Vichayasan/controller-AE-kit/Firmware/logo_mod.py

# logo_mod.py - Startup logo converted from logo.png for ST7567 128x64 LCD

try:
    import time
except ImportError:
    time = None

LOGO_W = 64
TEXT_X = 68
TEXT_Y = 17
TEXT_GAP = 8

LOGO_LEFT_BITMAP = bytes((
    0x00, 0x00, 0x00, 0x00, 0x00, 0x00, 0x00, 0x00, 0x00, 0x00, 0x00, 0x00, 0x00, 0x00, 0x00, 0x00,
    0x00, 0x00, 0x00, 0x00, 0x00, 0x00, 0x00, 0x00, 0x00, 0x00, 0x00, 0x00, 0x00, 0x00, 0x00, 0x00,
    0x00, 0x00, 0x00, 0x00, 0x00, 0x00, 0x00, 0x00, 0x00, 0x00, 0x00, 0x00, 0x00, 0x00, 0x00, 0x00,
    0x00, 0x00, 0x00, 0x00, 0x00, 0x00, 0x00, 0x00, 0x00, 0x00, 0x00, 0x00, 0x00, 0x00, 0x00, 0x00,
    0x00, 0x00, 0x00, 0x00, 0x00, 0x00, 0x00, 0x00, 0x00, 0x00, 0x00, 0x00, 0x00, 0x80, 0xC0, 0xE0,
    0xE0, 0xC0, 0x80, 0x80, 0x00, 0x00, 0x00, 0x00, 0x00, 0x30, 0x70, 0xF0, 0xF0, 0xF0, 0xF0, 0xF0,
    0xF0, 0xF0, 0xF0, 0xF0, 0xF0, 0xF0, 0xF0, 0xF0, 0xF0, 0xF0, 0xF0, 0xF0, 0xF0, 0xF0, 0xF0, 0xF0,
    0xF0, 0xF0, 0xE0, 0xE0, 0xC0, 0x80, 0x00, 0x00, 0x00, 0x00, 0x00, 0x00, 0x00, 0x00, 0x00, 0x00,
    0x00, 0x00, 0x00, 0x80, 0xC0, 0xE0, 0xC0, 0x80, 0x84, 0x84, 0x80, 0xC0, 0xE0, 0xF1, 0xE1, 0xC3,
    0x87, 0x83, 0x81, 0xC0, 0xE0, 0xF6, 0xF8, 0xF8, 0xF0, 0xE0, 0xC0, 0x80, 0x01, 0x03, 0x07, 0x0F,
    0x1F, 0x3F, 0x7F, 0x7F, 0x7F, 0x7F, 0x7F, 0x7F, 0x7F, 0x7F, 0x7F, 0x7F, 0x7F, 0x7F, 0x7F, 0x7F,
    0xFF, 0xFF, 0xFF, 0xFF, 0xFF, 0xFF, 0xFF, 0xFE, 0xFC, 0xF8, 0xF0, 0xC0, 0x00, 0x00, 0x00, 0x00,
    0x00, 0x00, 0x00, 0x00, 0x01, 0x01, 0x01, 0x00, 0x80, 0x80, 0x80, 0x01, 0x33, 0x7B, 0x33, 0x01,
    0x00, 0x80, 0xC0, 0xE0, 0xC1, 0x83, 0x07, 0x0F, 0x07, 0x33, 0x79, 0x78, 0x30, 0x00, 0x00, 0x00,
    0x00, 0x00, 0x00, 0x00, 0x00, 0x00, 0x00, 0x00, 0x80, 0xC0, 0xE0, 0xF0, 0xF8, 0xFC, 0xFE, 0xFF,
    0xFF, 0xFF, 0xFF, 0xFF, 0xFF, 0x7F, 0x3F, 0x0F, 0x07, 0x03, 0x01, 0x00, 0x00, 0x00, 0x00, 0x00,
    0x00, 0x00, 0x00, 0x00, 0x00, 0x00, 0x00, 0x07, 0x0F, 0x1F, 0x0F, 0x07, 0x02, 0x32, 0x02, 0x06,
    0x0F, 0x1F, 0x3F, 0x3F, 0x1F, 0x8F, 0x87, 0x02, 0x00, 0x30, 0x00, 0x00, 0x00, 0x00, 0x06, 0x0C,
    0x1C, 0x3C, 0x7C, 0xFC, 0xFC, 0xFE, 0xFF, 0xFF, 0xFF, 0xFF, 0xFF, 0xFF, 0xFF, 0xFB, 0xF3, 0xE3,
    0xC3, 0x03, 0x03, 0x01, 0x00, 0x00, 0x00, 0x00, 0x00, 0x00, 0x00, 0x00, 0x00, 0x00, 0x00, 0x00,
    0x00, 0x00, 0x00, 0x00, 0x00, 0x00, 0x00, 0x00, 0x00, 0x00, 0x00, 0x00, 0x00, 0x00, 0x00, 0x00,
    0x00, 0x80, 0x80, 0x86, 0x0F, 0x1F, 0x1F, 0x0F, 0x86, 0xC0, 0xC0, 0x80, 0x06, 0x07, 0x06, 0x80,
    0xC0, 0xE0, 0xE0, 0xC0, 0x81, 0x03, 0x0F, 0x1F, 0x3F, 0x7F, 0xFF, 0xFF, 0xFF, 0xFF, 0xFF, 0xFF,
    0xFF, 0xFF, 0xFE, 0xFC, 0xF8, 0xF0, 0xE0, 0xC0, 0x80, 0x00, 0x00, 0x00, 0x00, 0x00, 0x00, 0x00,
    0x00, 0x00, 0x00, 0x00, 0x00, 0x00, 0x00, 0x00, 0x00, 0x00, 0x00, 0x00, 0x00, 0x00, 0x00, 0x00,
    0x00, 0x01, 0x03, 0x01, 0x01, 0x01, 0x01, 0x01, 0x01, 0x03, 0x03, 0x01, 0x01, 0x01, 0x01, 0x01,
    0x03, 0x07, 0x07, 0x03, 0x01, 0x00, 0x04, 0x00, 0x00, 0x00, 0x00, 0x01, 0x03, 0x07, 0x0F, 0x0F,
    0x0F, 0x0F, 0x0F, 0x0F, 0x0F, 0x0F, 0x0F, 0x0F, 0x0F, 0x0F, 0x0E, 0x0C, 0x00, 0x00, 0x00, 0x00,
    0x00, 0x00, 0x00, 0x00, 0x00, 0x00, 0x00, 0x00, 0x00, 0x00, 0x00, 0x00, 0x00, 0x00, 0x00, 0x00,
    0x00, 0x00, 0x00, 0x00, 0x00, 0x00, 0x00, 0x00, 0x00, 0x00, 0x00, 0x00, 0x00, 0x00, 0x00, 0x00,
    0x00, 0x00, 0x00, 0x00, 0x00, 0x00, 0x00, 0x00, 0x00, 0x00, 0x00, 0x00, 0x00, 0x00, 0x00, 0x00,
    0x00, 0x00, 0x00, 0x00, 0x00, 0x00, 0x00, 0x00, 0x00, 0x00, 0x00, 0x00, 0x00, 0x00, 0x00, 0x00,
))

_FONT = {
    "A": ("010", "101", "111", "101", "101"),
    "C": ("111", "100", "100", "100", "111"),
    "D": ("110", "101", "101", "101", "110"),
    "E": ("111", "100", "110", "100", "111"),
    "I": ("111", "010", "010", "010", "111"),
    "L": ("100", "100", "100", "100", "111"),
    "N": ("101", "111", "111", "111", "101"),
    "O": ("111", "101", "101", "101", "111"),
    "P": ("110", "101", "110", "100", "100"),
    "R": ("110", "101", "110", "101", "101"),
    "S": ("111", "100", "111", "001", "111"),
    "T": ("111", "010", "010", "010", "010"),
    "U": ("101", "101", "101", "101", "111"),
    "X": ("101", "101", "010", "101", "101"),
}


def _tiny_text(lcd, text, x, y, color=1, scale=1):
    for ch in text:
        if ch == " ":
            x += 2 * scale
            continue
        glyph = _FONT.get(ch)
        if glyph is None:
            x += 4 * scale
            continue
        for row, pattern in enumerate(glyph):
            for col, pixel in enumerate(pattern):
                if pixel == "1":
                    for dy in range(scale):
                        for dx in range(scale):
                            lcd.pixel(x + col * scale + dx, y + row * scale + dy, color)
        x += 4 * scale


def _draw_left_logo(lcd):
    for page in range(8):
        base = page * LOGO_W
        y0 = page * 8
        for x in range(LOGO_W):
            b = LOGO_LEFT_BITMAP[base + x]
            for bit in range(8):
                if b & (1 << bit):
                    lcd.pixel(x, y0 + bit, 1)


def draw(lcd):
    lcd.fill(0)
    _draw_left_logo(lcd)
    _tiny_text(lcd, "REPCO NEX", TEXT_X, TEXT_Y)
    _tiny_text(lcd, "INDUSTRIAL", TEXT_X, TEXT_Y + TEXT_GAP)
    _tiny_text(lcd, "SOLUTIONS", TEXT_X, TEXT_Y + TEXT_GAP * 2)


def show(lcd, update=None, hold_ms=1200):
    draw(lcd)
    if update is not None:
        update()
    if hold_ms and time is not None:
        time.sleep_ms(hold_ms)
